Badbird5907/makropad/PCB/Components/N0016A.stp

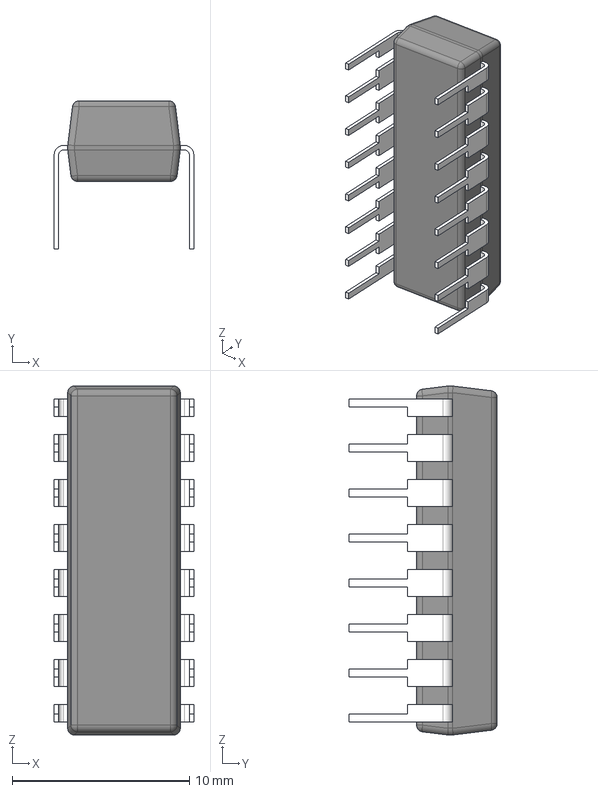
[picture p15: CAD file, 2025-01-31]
PCB/Components/N0016A.stp
7.87 x 8.37 x 19.7 mm
BODY_N0016A_AF0
LEAD_N0016A_AF1
LEAD_N0016A x 10
LEAD_N0016A_AF3
LEAD_N0016A_AF5
LEAD_N0016A_AF0
LEAD_N0016A_AF2
LEAD_N0016A_AF4
