Badbird5907/makropad/PCB/Components/PCF8574A_SMD.step

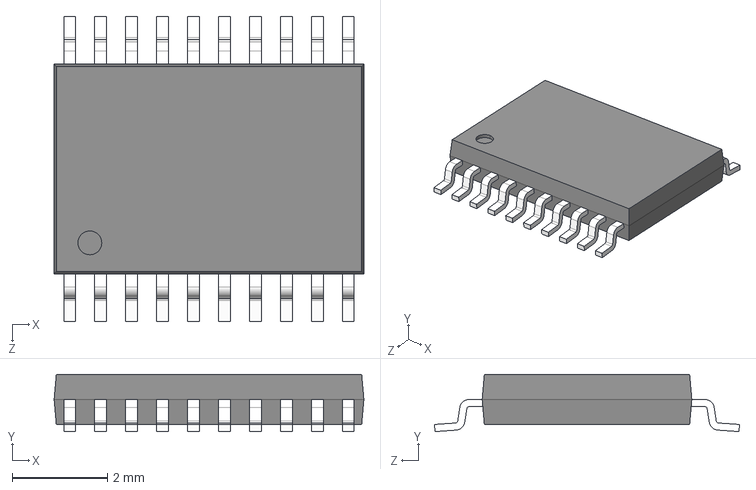
[picture p16: CAD file, 2025-01-31]
PCB/Components/PCF8574A_SMD.step
6.50 x 1.20 x 6.40 mm
